baskentbitirme/VR-Assisted-Robotic-Surgery-System/Example Images/IMG_3954_JPG.rf.64349f993c886a088b1cc4ce679b4b38.jpg

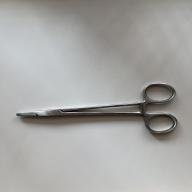
Example Images/IMG_3954_JPG.rf.64349f993c886a088b1cc4ce679b4b38.jpg
