baskentbitirme/VR-Assisted-Robotic-Surgery-System/Example Images/IMG_3955_JPG.rf.8ee6fed497507000e4d3afec2221d7da.jpg

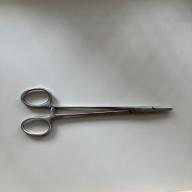
Example Images/IMG_3955_JPG.rf.8ee6fed497507000e4d3afec2221d7da.jpg
