baskentbitirme/VR-Assisted-Robotic-Surgery-System/Example Images/IMG_3961_JPG.rf.d04355e1fcb8ea456c4a17d2488a1ab5.jpg

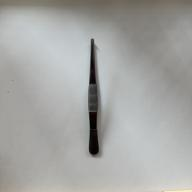
Example Images/IMG_3961_JPG.rf.d04355e1fcb8ea456c4a17d2488a1ab5.jpg
