baskentbitirme/VR-Assisted-Robotic-Surgery-System/Example Images/IMG_3975_JPG.rf.fb13b953f81e80a28ee053751937d0c0.jpg

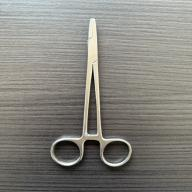
Example Images/IMG_3975_JPG.rf.fb13b953f81e80a28ee053751937d0c0.jpg
