baskentbitirme/VR-Assisted-Robotic-Surgery-System/Example Images/IMG_3987_JPG.rf.4e3649affe6cfbedf9ce9c6ee356bd7c.jpg

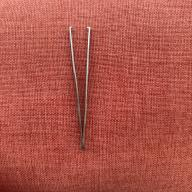
Example Images/IMG_3987_JPG.rf.4e3649affe6cfbedf9ce9c6ee356bd7c.jpg
