baskentbitirme/VR-Assisted-Robotic-Surgery-System/Example Images/IMG_3998_JPG.rf.bec77673ba1f2f0b0fd8b94f01dce2d3.jpg

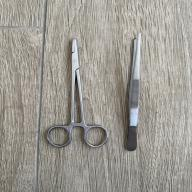
Example Images/IMG_3998_JPG.rf.bec77673ba1f2f0b0fd8b94f01dce2d3.jpg
