baskentbitirme/VR-Assisted-Robotic-Surgery-System/Example Images/IMG_4008_JPG.rf.c4d5e19fd2dbbaf42c431c0944eb0481.jpg

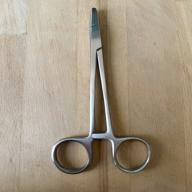
Example Images/IMG_4008_JPG.rf.c4d5e19fd2dbbaf42c431c0944eb0481.jpg
