baskentbitirme/VR-Assisted-Robotic-Surgery-System/Example Images/IMG_4011_JPG.rf.78541476219cf846eccabdaba2cbb438.jpg

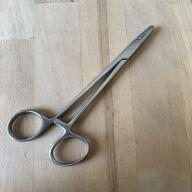
Example Images/IMG_4011_JPG.rf.78541476219cf846eccabdaba2cbb438.jpg
