baskentbitirme/VR-Assisted-Robotic-Surgery-System/Example Images/IMG_4015_JPG.rf.94c088a03cb776983faa5dfd93c8df1a.jpg

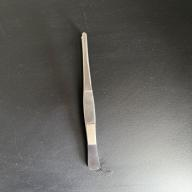
Example Images/IMG_4015_JPG.rf.94c088a03cb776983faa5dfd93c8df1a.jpg
