baskentbitirme/VR-Assisted-Robotic-Surgery-System/Example Images/IMG_4033_JPG.rf.da3d5c6ce3c566d4e81afef778d92bca.jpg

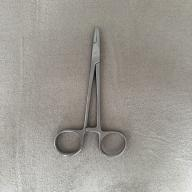
Example Images/IMG_4033_JPG.rf.da3d5c6ce3c566d4e81afef778d92bca.jpg
