baskentbitirme/VR-Assisted-Robotic-Surgery-System/Example Images/IMG_4038_JPG.rf.f1f5d9deec4ad07f405fbded659bcda4.jpg

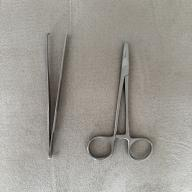
Example Images/IMG_4038_JPG.rf.f1f5d9deec4ad07f405fbded659bcda4.jpg
