baskentbitirme/VR-Assisted-Robotic-Surgery-System/Example Images/IMG_4053_JPG.rf.ef0b01e9af4377976dd0a75bce934050.jpg

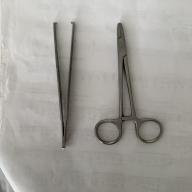
Example Images/IMG_4053_JPG.rf.ef0b01e9af4377976dd0a75bce934050.jpg
