baskentbitirme/VR-Assisted-Robotic-Surgery-System/Example Images/IMG_4072_JPG.rf.bc49606dbce4a738fbdb766e20abf860.jpg

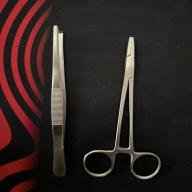
Example Images/IMG_4072_JPG.rf.bc49606dbce4a738fbdb766e20abf860.jpg
