baskentbitirme/VR-Assisted-Robotic-Surgery-System/Example Images/IMG_4075_JPG.rf.479165e9181e6099c134d8a9de64464b.jpg

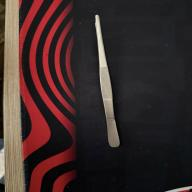
Example Images/IMG_4075_JPG.rf.479165e9181e6099c134d8a9de64464b.jpg
