baskentbitirme/VR-Assisted-Robotic-Surgery-System/Example Images/IMG_4081_JPG.rf.e43bb2edacd407c3f25558633a18493a.jpg

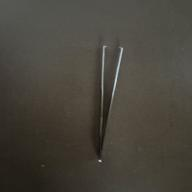
Example Images/IMG_4081_JPG.rf.e43bb2edacd407c3f25558633a18493a.jpg
