baskentbitirme/VR-Assisted-Robotic-Surgery-System/Example Images/IMG_4093_JPG.rf.6b826b724cdf39542dfb44c4d1d559cf.jpg

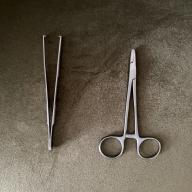
Example Images/IMG_4093_JPG.rf.6b826b724cdf39542dfb44c4d1d559cf.jpg
