baskentbitirme/VR-Assisted-Robotic-Surgery-System/Example Images/IMG_4098_JPG.rf.a3765a5683bce949dc686ef2a8f9485f.jpg

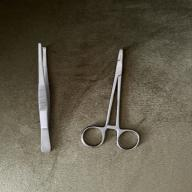
Example Images/IMG_4098_JPG.rf.a3765a5683bce949dc686ef2a8f9485f.jpg
