baskentbitirme/VR-Assisted-Robotic-Surgery-System/Example Images/IMG_4108_JPG.rf.d5485ecb897bc96bf68dd3c3737cc458.jpg

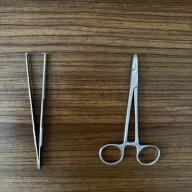
Example Images/IMG_4108_JPG.rf.d5485ecb897bc96bf68dd3c3737cc458.jpg
