baskentbitirme/VR-Assisted-Robotic-Surgery-System/Example Images/IMG_4127_JPG.rf.5e8a780be0e1a154979bcb4125f75b1a.jpg

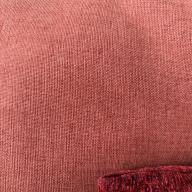
Example Images/IMG_4127_JPG.rf.5e8a780be0e1a154979bcb4125f75b1a.jpg
