baskentbitirme/VR-Assisted-Robotic-Surgery-System/Example Images/IMG_4134_JPG.rf.497e2e090e73e56da7602515bd3fed5c.jpg

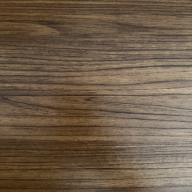
Example Images/IMG_4134_JPG.rf.497e2e090e73e56da7602515bd3fed5c.jpg
