baskentbitirme/VR-Assisted-Robotic-Surgery-System/Unity/Assets/Modellerim/Aletler/textures/internal_ground_ao_texture.jpeg

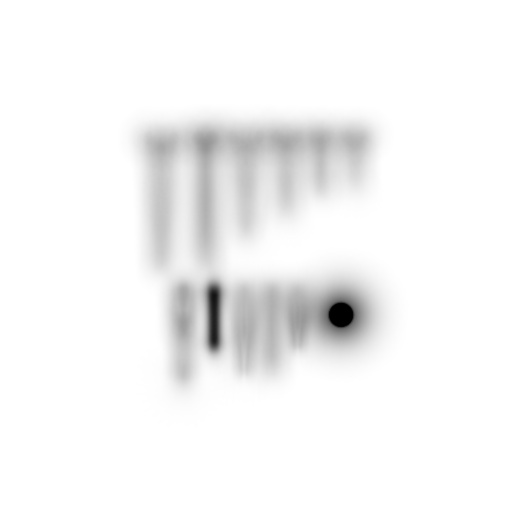
Unity/Assets/Modellerim/Aletler/textures/internal_ground_ao_texture.jpeg
