baskentbitirme/VR-Assisted-Robotic-Surgery-System/Unity/Assets/Modellerim/Aletler/textures/Tray_MAT_AO.jpeg

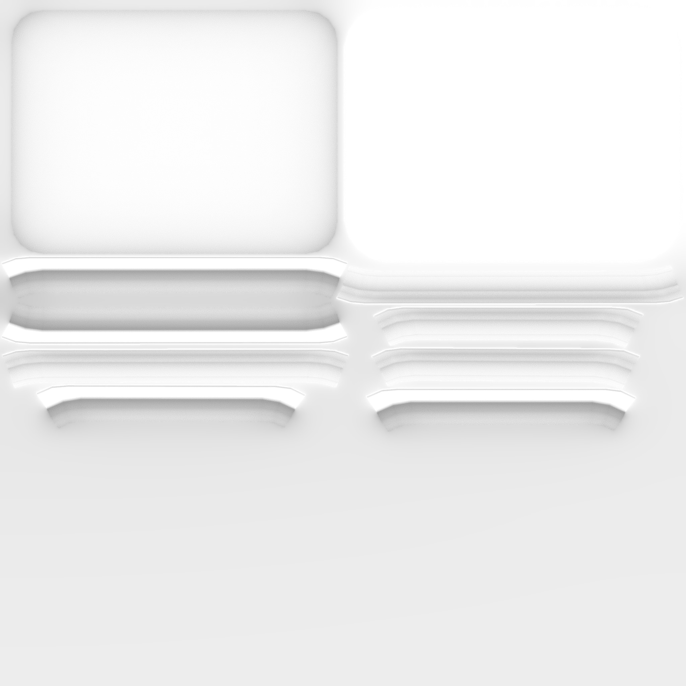
Unity/Assets/Modellerim/Aletler/textures/Tray_MAT_AO.jpeg
