baskentbitirme/VR-Assisted-Robotic-Surgery-System/Unity/Assets/Modellerim/Aletler/textures/Tray_MAT_roughness.jpeg

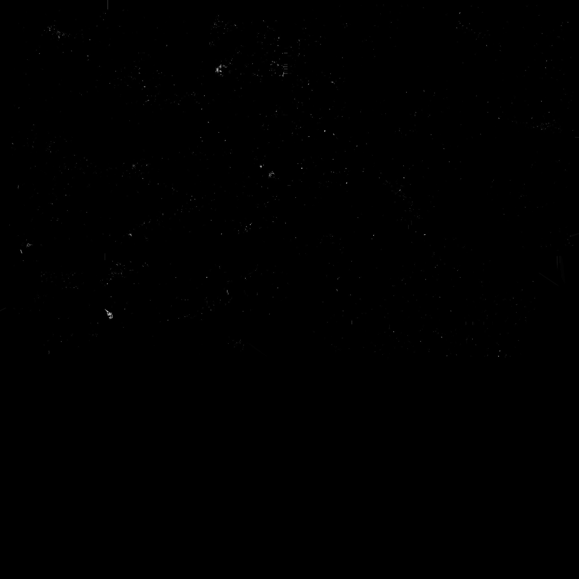
Unity/Assets/Modellerim/Aletler/textures/Tray_MAT_roughness.jpeg
