baskentbitirme/VR-Assisted-Robotic-Surgery-System/Unity/Assets/Modellerim/Masalar/textures/internal_ground_ao_texture.jpeg

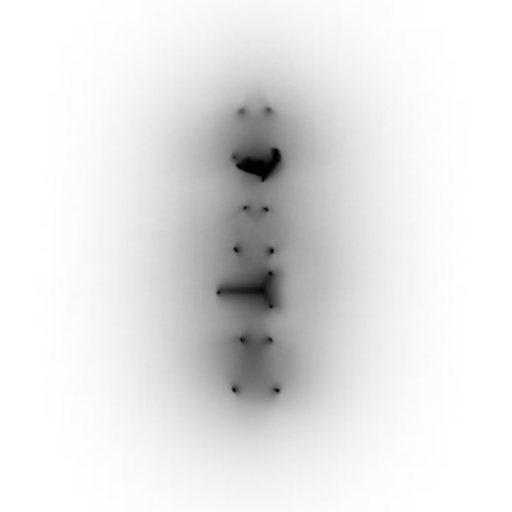
Unity/Assets/Modellerim/Masalar/textures/internal_ground_ao_texture.jpeg
