baskentbitirme/VR-Assisted-Robotic-Surgery-System/Unity/Assets/Modellerim/realistic-surgical-glove-with-folds-texture/source/model/model/textures/Nurse__Body_Low_roughness.jpg

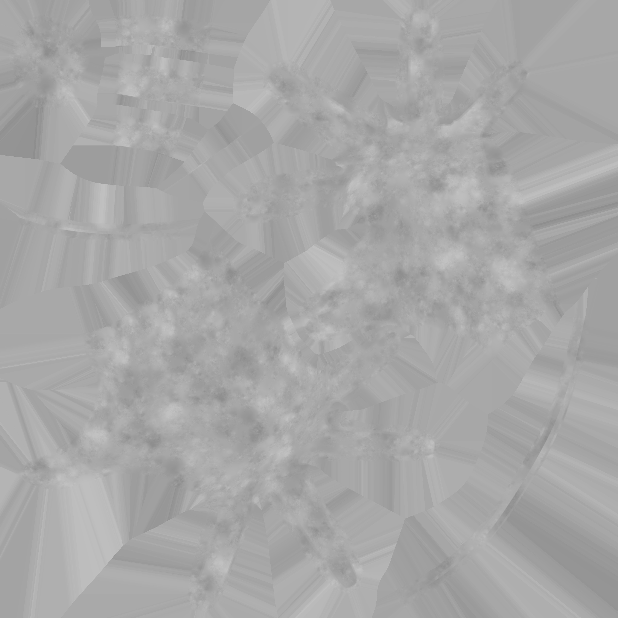
Unity/Assets/Modellerim/realistic-surgical-glove-with-folds-texture/source/model/model/textures/Nurse__Body_Low_roughness.jpg
