baskentbitirme/VR-Assisted-Robotic-Surgery-System/Unity/Assets/Samples/XR Interaction Toolkit/3.3.1/Starter Assets/DemoSceneAssets/Sprites/Circle_60x60_Horizontal.png

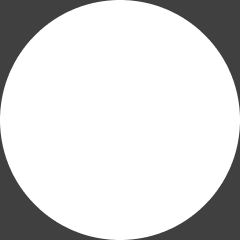
Unity/Assets/Samples/XR Interaction Toolkit/3.3.1/Starter Assets/DemoSceneAssets/Sprites/Circle_60x60_Horizontal.png
