baskentbitirme/VR-Assisted-Robotic-Surgery-System/Unity/Assets/Samples/XR Interaction Toolkit/3.3.1/Starter Assets/DemoSceneAssets/Sprites/Round Radius 4 Outline.png

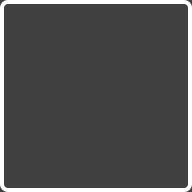
Unity/Assets/Samples/XR Interaction Toolkit/3.3.1/Starter Assets/DemoSceneAssets/Sprites/Round Radius 4 Outline.png
