baskentbitirme/VR-Assisted-Robotic-Surgery-System/Unity/Assets/Sprites/ChatGPT Image 26 Nis 2026 21_11_31.png

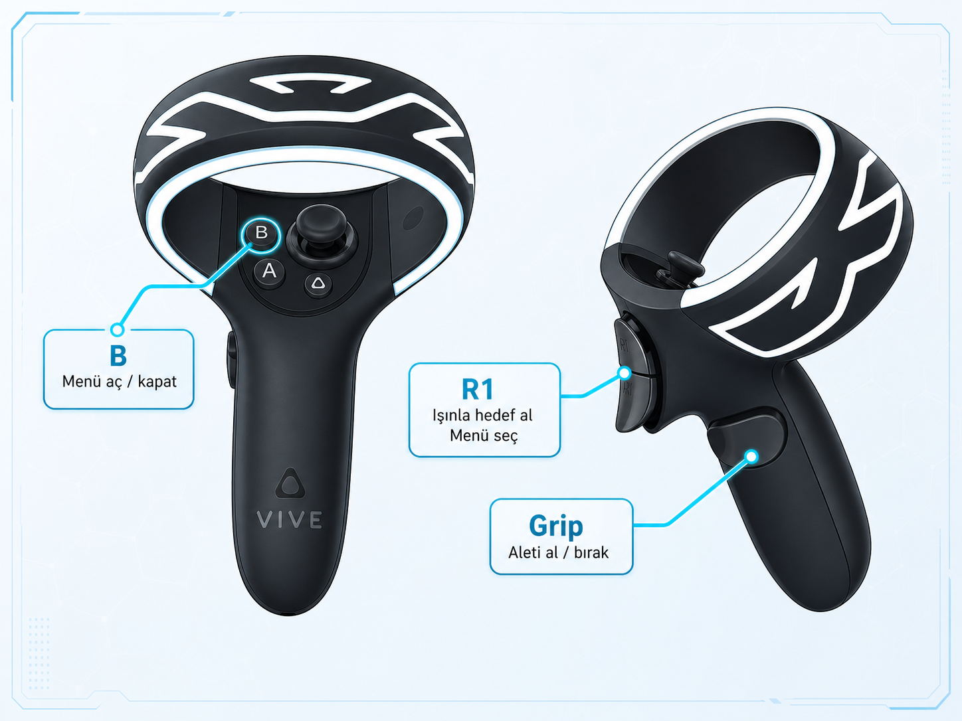
Unity/Assets/Sprites/ChatGPT Image 26 Nis 2026 21_11_31.png
