baskentbitirme/VR-Assisted-Robotic-Surgery-System/Unity/Assets/Sprites/Giris_Ekrani.png

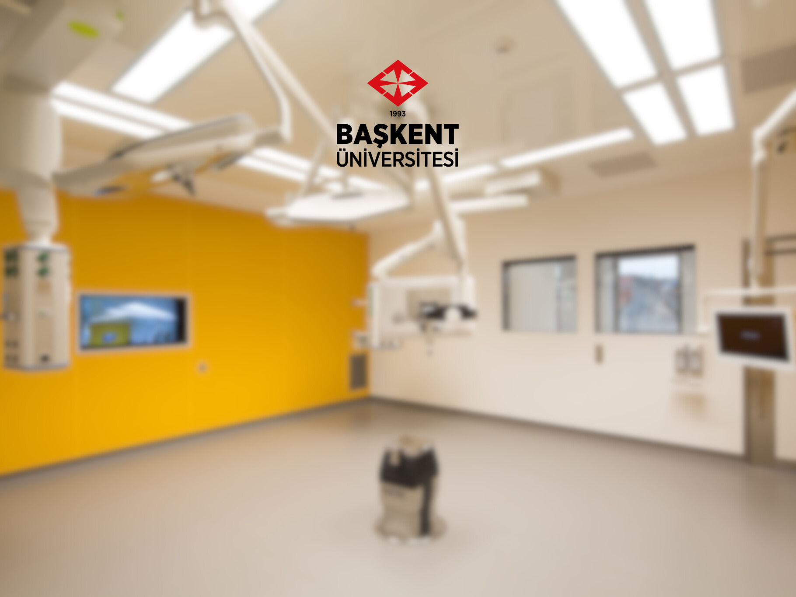
Unity/Assets/Sprites/Giris_Ekrani.png
