baskentbitirme/VR-Assisted-Robotic-Surgery-System/Unity/Assets/Modellerim/Masalar/source/Surgical_Table_Single_Collection/Surgical_Table_Double.jpg

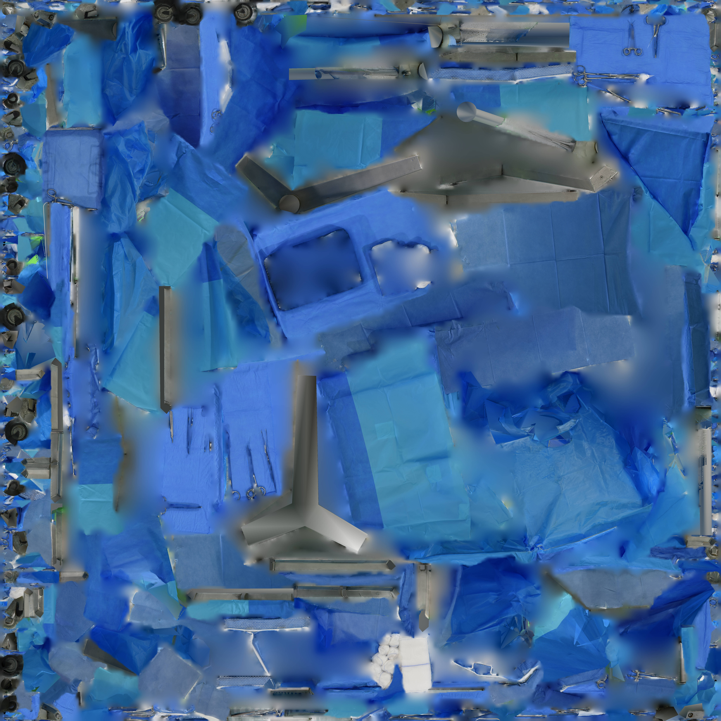
Unity/Assets/Modellerim/Masalar/source/Surgical_Table_Single_Collection/Surgical_Table_Double.jpg
