baskentbitirme/VR-Assisted-Robotic-Surgery-System/Unity/Assets/Modellerim/Oda_Charite/source/charite-university-hospital-operating-room(1)/source/OP_Mitte/Volumetric_OR_Room1.jpg

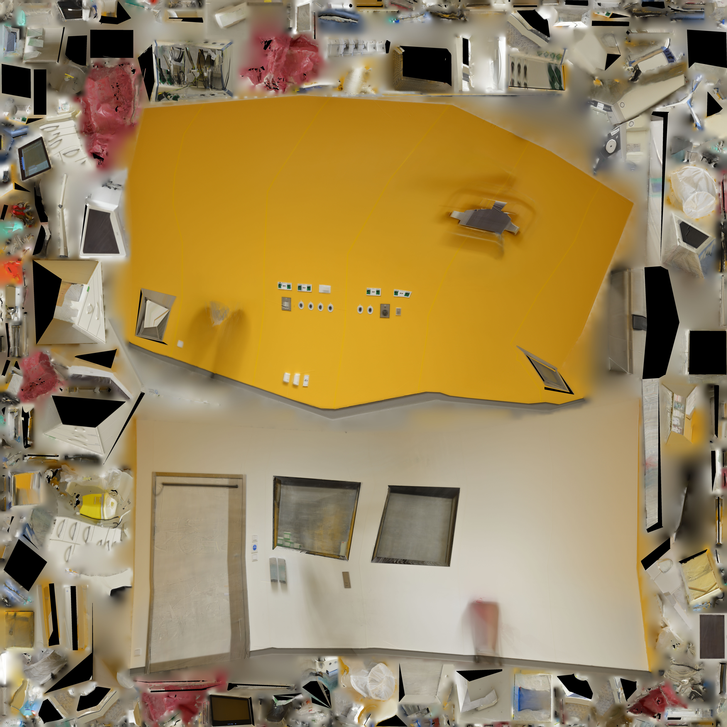
Unity/Assets/Modellerim/Oda_Charite/source/charite-university-hospital-operating-room(1)/source/OP_Mitte/Volumetric_OR_Room1.jpg
